derekfountain/zx-spectrum-pico-rom/images/first_fail.jpg

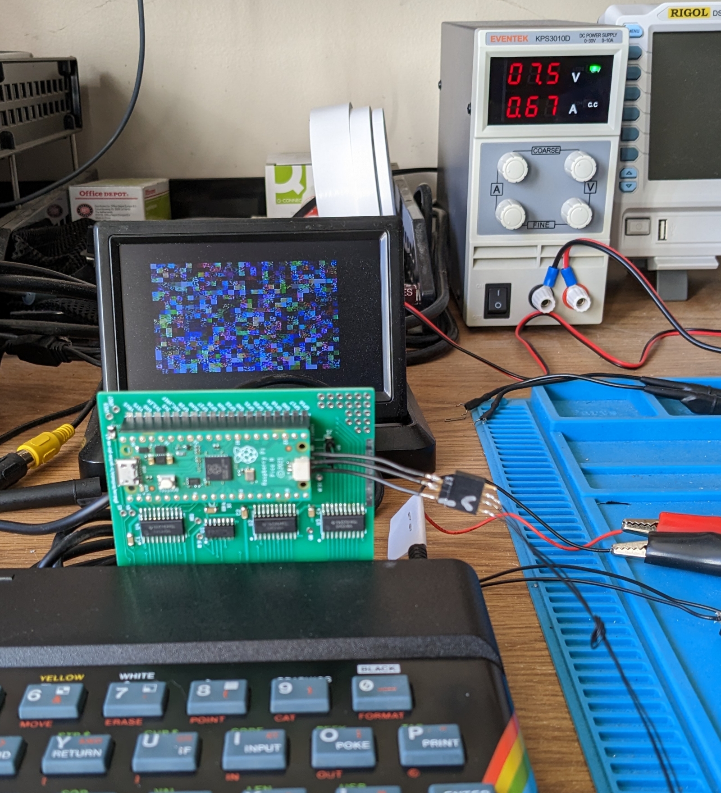
images/first_fail.jpg
