derekfountain/zx-spectrum-pico-rom/images/first_success.jpg

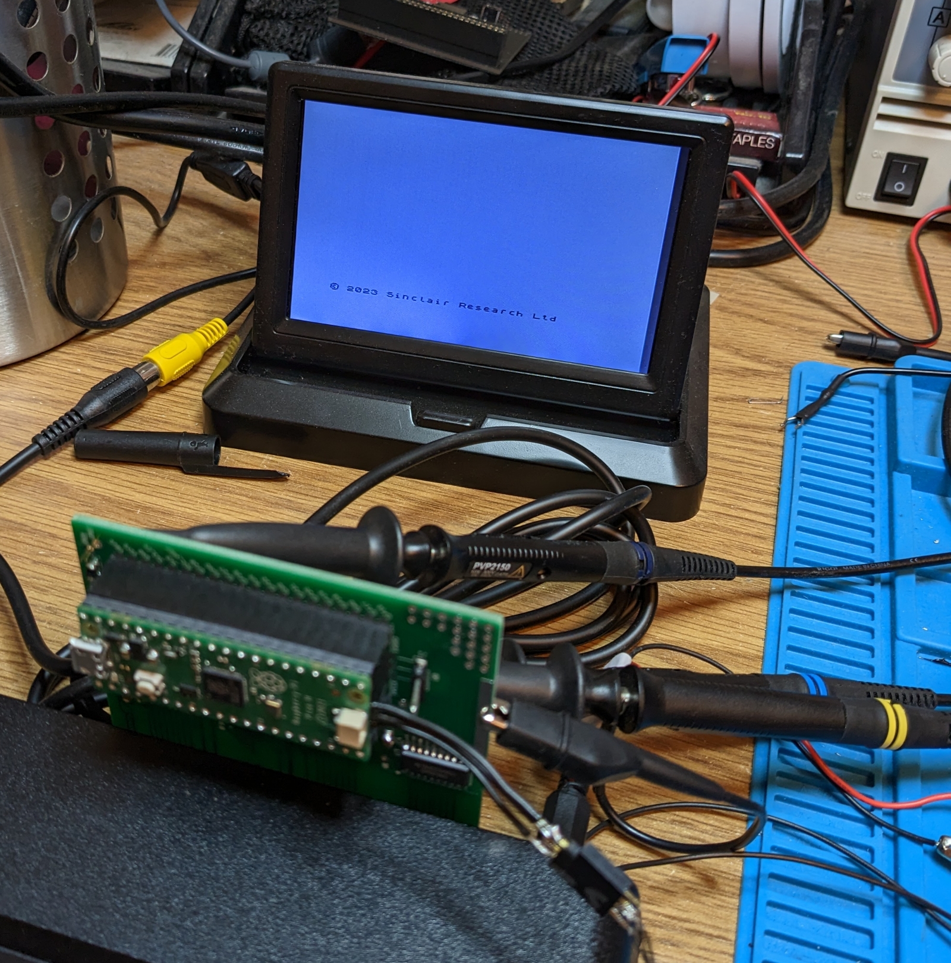
images/first_success.jpg
