derekfountain/zx-spectrum-pico-rom/images/frame_trace_nmi_original.png

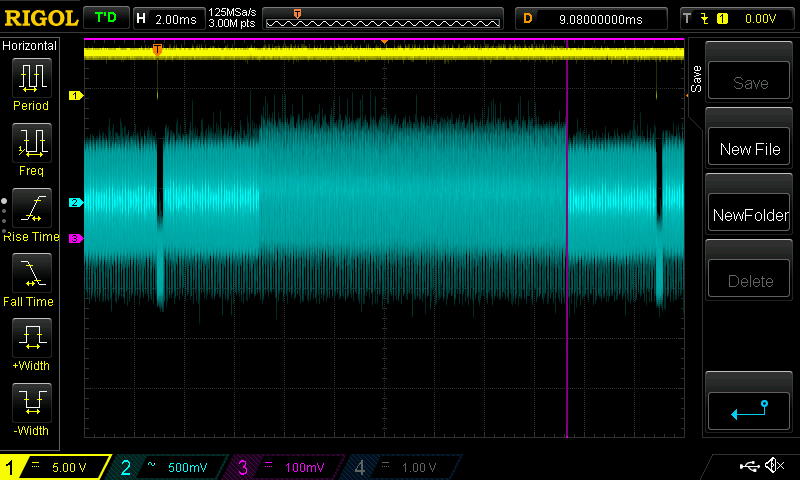
images/frame_trace_nmi_original.png
