derekfountain/zx-spectrum-pico-rom/images/frame_trace_unannotated.png

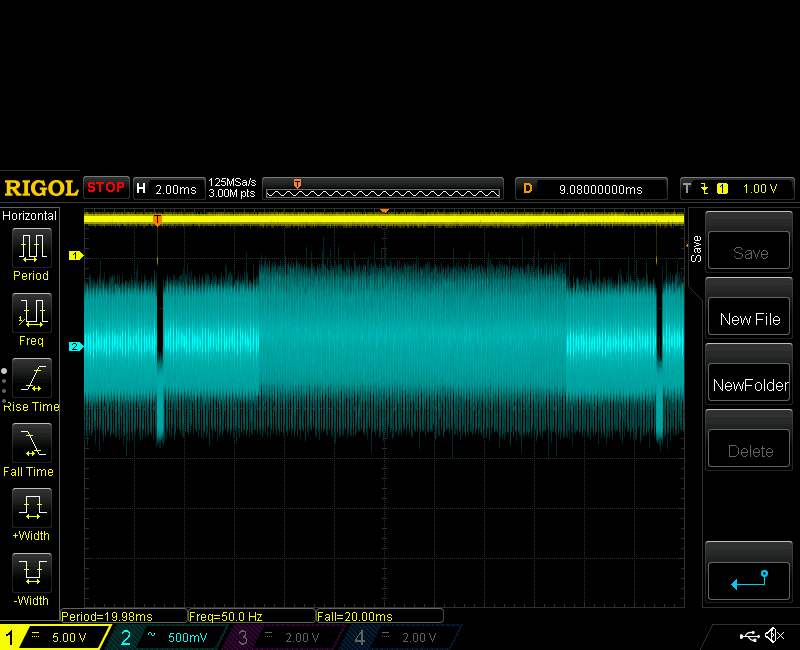
images/frame_trace_unannotated.png
