derekfountain/zx-spectrum-pico-rom/images/PXL_20230126_151511144.jpg

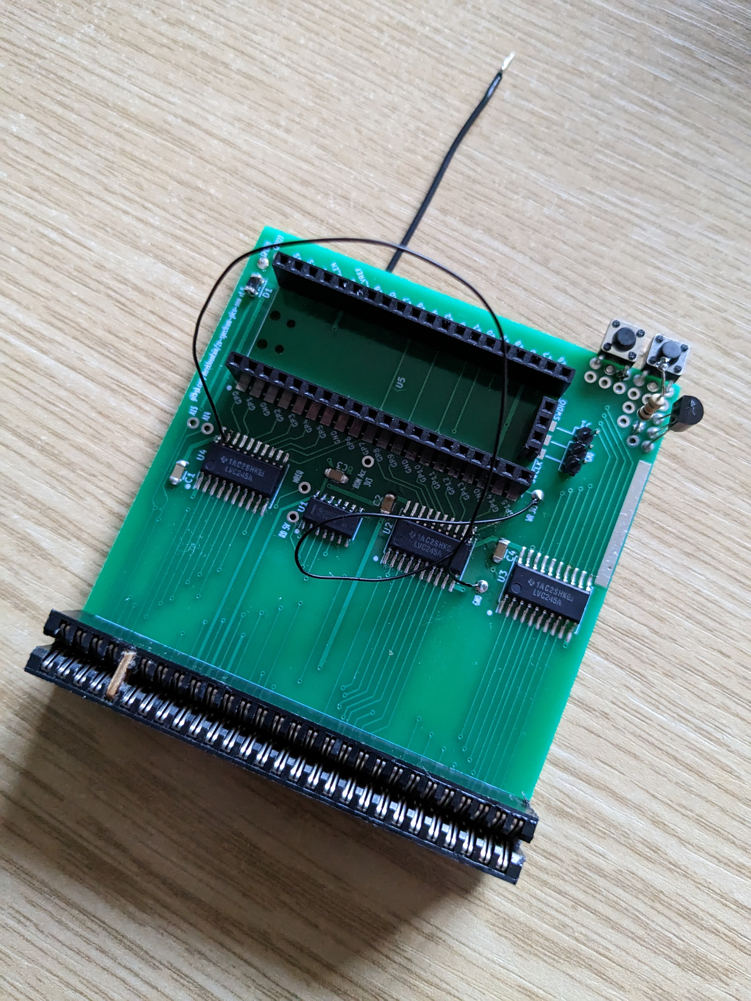
images/PXL_20230126_151511144.jpg
