derekfountain/zx-spectrum-pico-rom/images/second_pcb.jpg

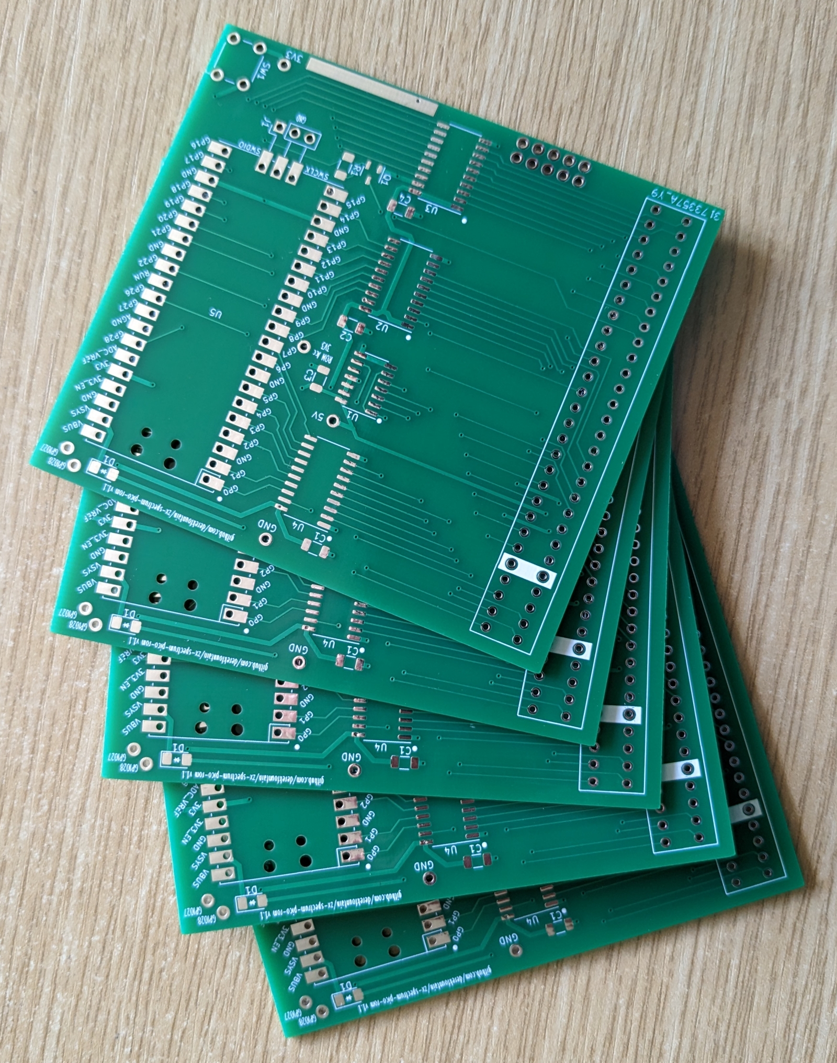
images/second_pcb.jpg
