derekfountain/zx-spectrum-pico-rom/images/second_version.jpg

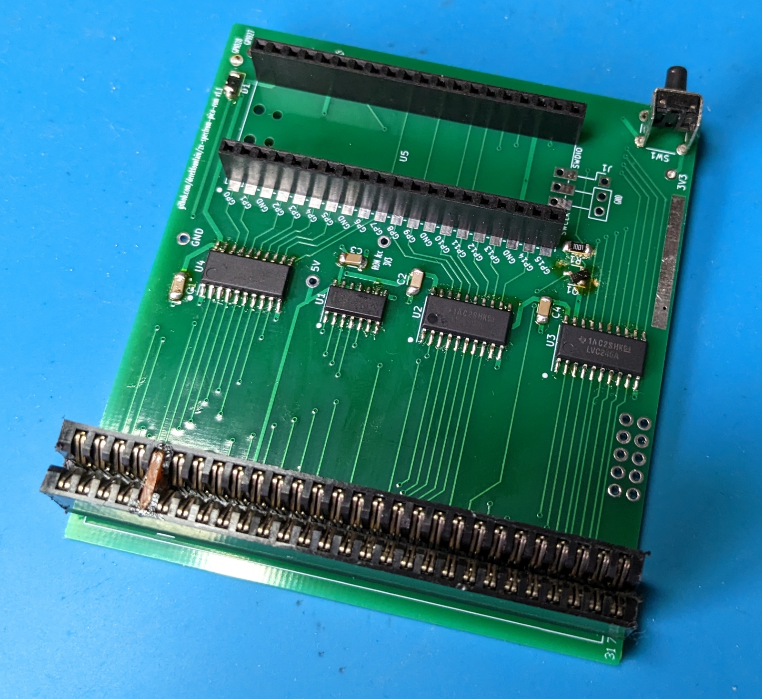
images/second_version.jpg
