derekfountain/zx-spectrum-pico-rom/srom/Images/board_complete.jpg

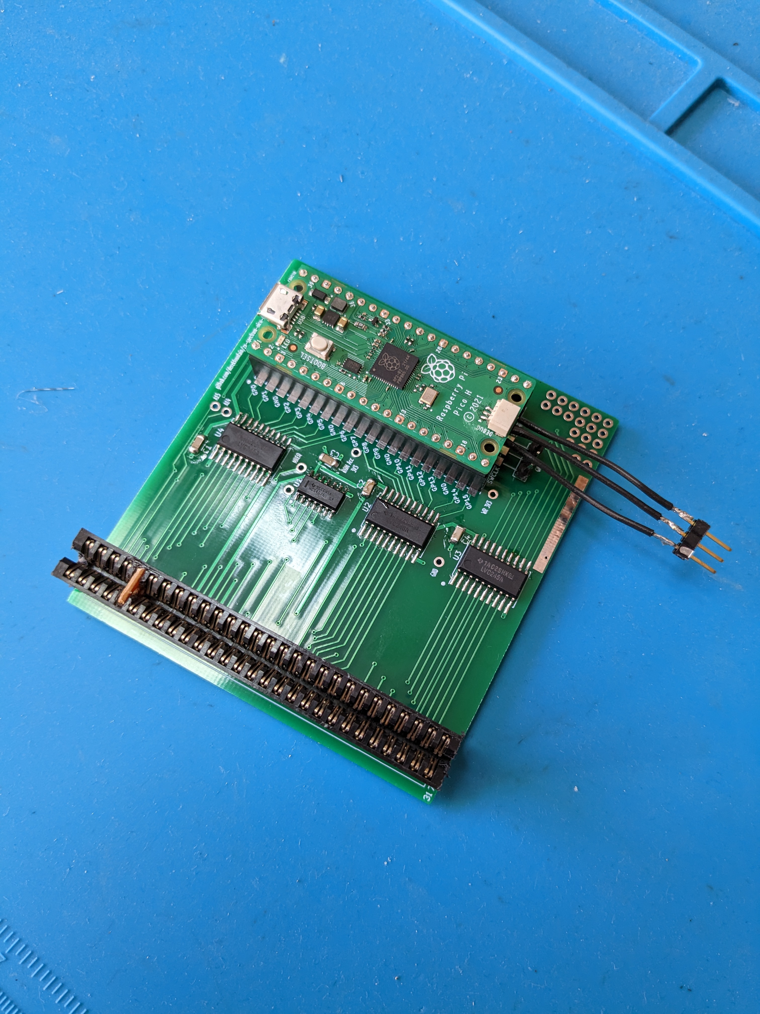
srom/Images/board_complete.jpg
