derekfountain/zx-spectrum-pico-rom/srom/Images/initial_board_powered.jpg

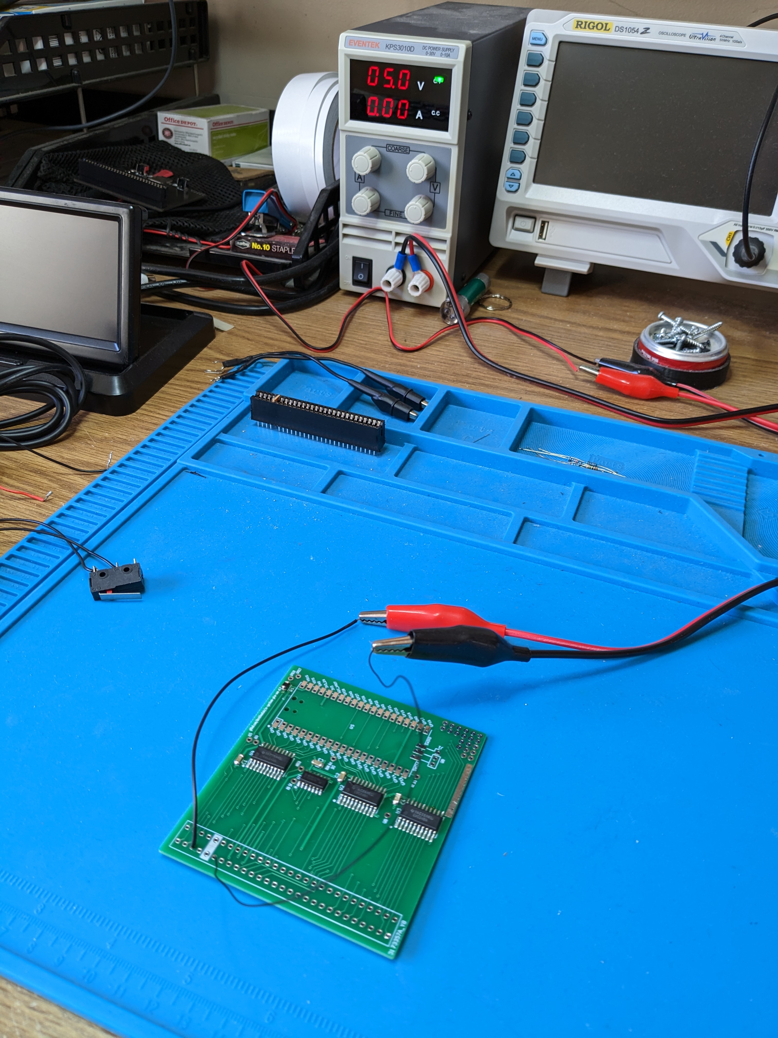
srom/Images/initial_board_powered.jpg
