derekfountain/zx-spectrum-pico-rom/srom/Images/mreq_timing.png

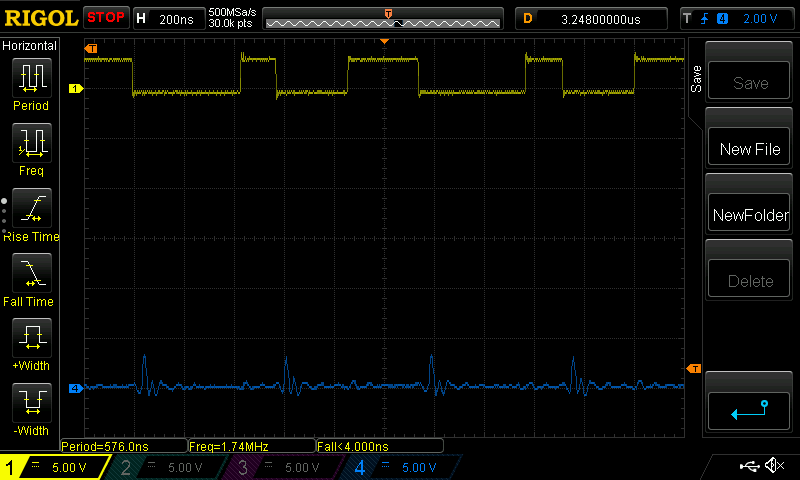
srom/Images/mreq_timing.png
