derekfountain/zx-spectrum-pico-rom/srom/Images/plugged_in_not_working.jpg

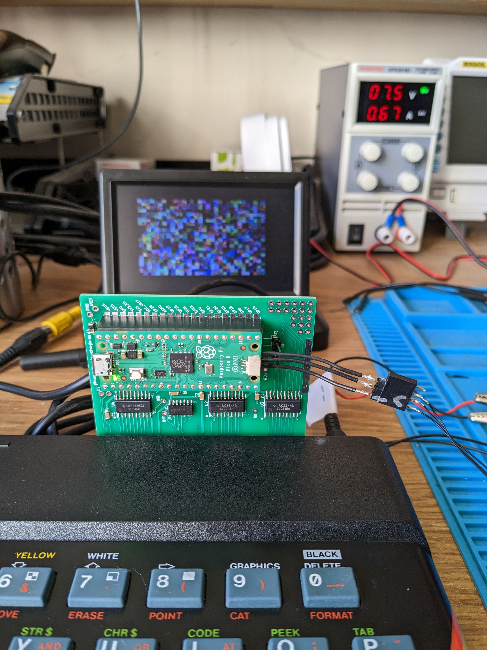
srom/Images/plugged_in_not_working.jpg
