derekfountain/zx-spectrum-pico-rom/images/first_test.jpg

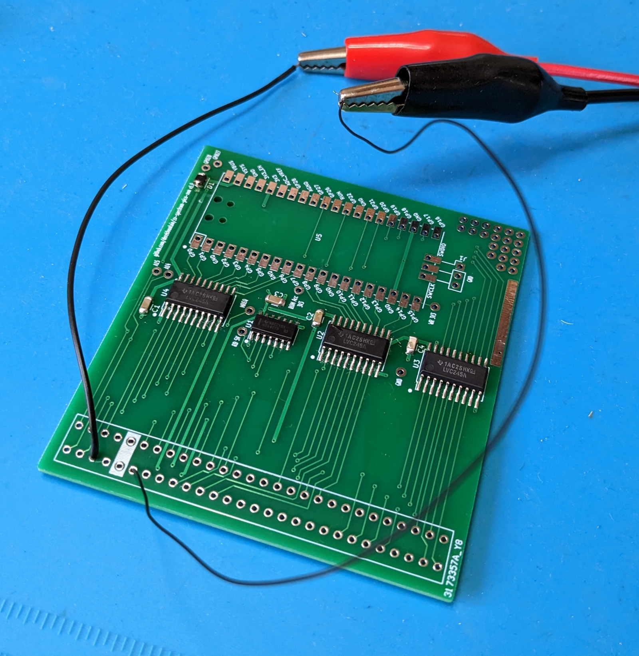
images/first_test.jpg
