derekfountain/zx-spectrum-pico-rom/firmware_nmi_lower_border/roms.h

unsigned char __ROMs_48_original_rom[] = {
  0xf3, 0xaf, 0x11, 0xff, 0xff, 0xc3, 0xcb, 0x11, 0x2a, 0x5d, 0x5c, 0x22,
  0x5f, 0x5c, 0x18, 0x43, 0xc3, 0xf2, 0x15, 0xff, 0xff, 0xff, 0xff, 0xff,
  0x2a, 0x5d, 0x5c, 0x7e, 0xcd, 0x7d, 0x00, 0xd0, 0xcd, 0x74, 0x00, 0x18,
  0xf7, 0xff, 0xff, 0xff, 0xc3, 0x5b, 0x33, 0xff, 0xff, 0xff, 0xff, 0xff,
  0xc5, 0x2a, 0x61, 0x5c, 0xe5, 0xc3, 0x9e, 0x16, 0xf5, 0xe5, 0x2a, 0x78,
  0x5c, 0x23, 0x22, 0x78, 0x5c, 0x7c, 0xb5, 0x20, 0x03, 0xfd, 0x34, 0x40,
  0xc5, 0xd5, 0xcd, 0xbf, 0x02, 0xd1, 0xc1, 0xe1, 0xf1, 0xfb, 0xc9, 0xe1,
  0x6e, 0xfd, 0x75, 0x00, 0xed, 0x7b, 0x3d, 0x5c, 0xc3, 0xc5, 0x16, 0xff,
  0xff, 0xff, 0xff, 0xff, 0xff, 0xff,

   245 ,                // push af
   62  , 3   ,          // ld a, 3
   211 , 254 ,          // out (254),a
   211 , 254 ,          // out (254), a
   62  , 7   ,          // ld a, 7
   211 , 254 ,          // out (254), a
   241 ,                // pop af

  0xed, 0x45,           // retn

                                                  0x2a, 0x5d, 0x5c, 0x23,
  0x22, 0x5d, 0x5c, 0x7e, 0xc9, 0xfe, 0x21, 0xd0, 0xfe, 0x0d, 0xc8, 0xfe,
  0x10, 0xd8, 0xfe, 0x18, 0x3f, 0xd8, 0x23, 0xfe, 0x16, 0x38, 0x01, 0x23,
  0x37, 0x22, 0x5d, 0x5c, 0xc9, 0xbf, 0x52, 0x4e, 0xc4, 0x49, 0x4e, 0x4b,
  0x45, 0x59, 0xa4, 0x50, 0xc9, 0x46, 0xce, 0x50, 0x4f, 0x49, 0x4e, 0xd4,
  0x53, 0x43, 0x52, 0x45, 0x45, 0x4e, 0xa4, 0x41, 0x54, 0x54, 0xd2, 0x41,
  0xd4, 0x54, 0x41, 0xc2, 0x56, 0x41, 0x4c, 0xa4, 0x43, 0x4f, 0x44, 0xc5,
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
  0xaf, 0xb0, 0xb1, 0xc0, 0xa7, 0xa6, 0xbe, 0xad, 0xb2, 0xba, 0xe5, 0xa5,
  0xc2, 0xe1, 0xb3, 0xb9, 0xc1, 0xb8, 0x7e, 0xdc, 0xda, 0x5c, 0xb7, 0x7b,
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
};
unsigned int __ROMs_48_original_rom_len = 16384;
unsigned char *roms[] = {
__ROMs_48_original_rom,
};
