derekfountain/zx-spectrum-pico-rom/firmware/roms.h

#if ZX_IF1_VERSION

unsigned char __ROMs_if1_rom[] = {
  0xe1, 0xfd, 0x36, 0x7c, 0x00, 0xc3, 0x00, 0x07, 0x2a, 0x5d, 0x5c, 0xe1,
  0xe5, 0xc3, 0x9a, 0x00, 0x22, 0xba, 0x5c, 0xe1, 0xd5, 0x18, 0x6a, 0xff,
  0xfd, 0xcb, 0x01, 0x7e, 0xc9, 0xff, 0xff, 0xff, 0xdf, 0x28, 0x45, 0x18,
  0x15, 0xff, 0xff, 0xff, 0xfd, 0xcb, 0x02, 0x9e, 0x18, 0x12, 0xff, 0xff,
  0xc3, 0xf7, 0x01, 0xff, 0xff, 0xff, 0xff, 0xff, 0xfb, 0xc9, 0xcd, 0x77,
  0x00, 0xc3, 0x60, 0x02, 0xdf, 0x28, 0x25, 0xcd, 0x77, 0x00, 0xcd, 0xb7,
  0x17, 0xfd, 0xcb, 0x7c, 0x4e, 0x28, 0x19, 0xfd, 0xcb, 0x7c, 0x66, 0x28,
  0x13, 0xfd, 0x7e, 0x00, 0xfe, 0x14, 0x20, 0x0c, 0x21, 0x00, 0x00, 0xe5,
  0xc7, 0xff, 0xff, 0xff, 0xff, 0xff, 0xed, 0x45, 0x2a, 0x5d, 0x5c, 0x22,
  0x5f, 0x5c, 0xed, 0x7b, 0x3d, 0x5c, 0x21, 0xc5, 0x16, 0xe5, 0xc7, 0xfd,
  0xcb, 0x7c, 0x56, 0xc8, 0xed, 0x7b, 0x3d, 0x5c, 0xc7, 0x5e, 0x23, 0x56,
  0xed, 0x53, 0xbd, 0x5c, 0x23, 0xe3, 0xeb, 0x21, 0x00, 0x00, 0xe5, 0x21,
  0x08, 0x00, 0xe5, 0x21, 0xb9, 0x5c, 0xe5, 0xc3, 0x00, 0x07, 0xf5, 0x7c,
  0xb5, 0x20, 0x06, 0xf1, 0xe1, 0x2a, 0xba, 0x5c, 0xc9, 0xd5, 0x11, 0xfe,
  0x15, 0xed, 0x52, 0xd1, 0x20, 0x0e, 0xf1, 0x21, 0x00, 0x07, 0xe5, 0x21,
  0x04, 0x00, 0x19, 0x5e, 0x23, 0x56, 0xeb, 0xe9, 0xf7, 0x3e, 0x01, 0xd3,
  0xf7, 0x3e, 0xee, 0xd3, 0xef, 0xf1, 0xe1, 0xf5, 0xd7, 0x7b, 0x00, 0x32,
  0x3a, 0x5c, 0xfe, 0xff, 0x20, 0x17, 0xfd, 0xcb, 0x7c, 0x4e, 0x28, 0x0f,
  0xfd, 0xcb, 0x0c, 0x7e, 0x28, 0x09, 0x2a, 0x59, 0x5c, 0x7e, 0xfe, 0xf7,
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
  0x20, 0x20, 0x20, 0x20, 0x20, 0x20, 0x20, 0x00, 0x00, 0x00, 0x00, 0x00,
  0x00, 0x00, 0x00, 0x00, 0x18, 0x18, 0x18, 0x18, 0x00, 0x18, 0x18, 0x00,
  0x6c, 0x6c, 0x48, 0x00, 0x00, 0x00, 0x00, 0x00, 0x36, 0x36, 0x7f, 0x36,
  0xfe, 0x6c, 0x6c, 0x00, 0x7c, 0xd6, 0xd0, 0x7c, 0x16, 0xd6, 0x7c, 0x00,
  0x70, 0xda, 0xdc, 0x78, 0x1e, 0x3b, 0x5b, 0x0e, 0x78, 0xcc, 0xc0, 0x76,
  0xdc, 0xcc, 0x76, 0x00, 0x30, 0x30, 0x20, 0x00, 0x00, 0x00, 0x00, 0x00,
  0x18, 0x30, 0x30, 0x30, 0x30, 0x30, 0x18, 0x00, 0x30, 0x18, 0x18, 0x18,
  0x18, 0x18, 0x30, 0x00, 0x00, 0x24, 0x18, 0x66, 0x18, 0x24, 0x00, 0x00,
  0x00, 0x18, 0x18, 0x7e, 0x18, 0x18, 0x00, 0x00, 0x00, 0x00, 0x00, 0x00,
  0x00, 0x18, 0x18, 0x10, 0x00, 0x00, 0x00, 0xfe, 0x00, 0x00, 0x00, 0x00,
  0x00, 0x00, 0x00, 0x00, 0x00, 0x18, 0x18, 0x00, 0x02, 0x06, 0x0c, 0x18,
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
};
const unsigned int sw_rom_len = 1210;


typedef struct _rom_image
{
  uint8_t  *rom_data;
  uint32_t  rom_size;
  uint8_t  *rom_switcher_label;
} ROM_IMAGE;


#if !ZX_IF1_VERSION

/*
 * This is the list of ROM images which are cycled, in sequence, as the
 * user presses the button for the next ROM
 */
const ROM_IMAGE cycle_roms[] =
{
  {__ROMs_48_original_rom,          __ROMs_48_original_rom_len ,
  "   Retroleum Diagnostics v59    "},

  {__ROMs_retroleum_diag_v59_rom,   __ROMs_retroleum_diag_v59_rom_len ,
  "   GOSH Wonderful ROM v1.32     "},

  {__ROMs_gosh_wonderful_1_32_rom,  __ROMs_gosh_wonderful_1_32_rom_len ,
  " Original ZX Spectrum ROM 1982  "},
};

#else

/*
 * ROMs aren't cycled in the Interface One version but they need to be
 * run through the conversion optimisations so they need to be in this
 * array.
 */
const ROM_IMAGE cycle_roms[] =
{
  {__ROMs_48_original_rom,          __ROMs_48_original_rom_len ,
  "                                "},

  {__ROMs_if1_rom,                  __ROMs_if1_rom_len ,
  "                                "},
};

#endif    /* Interface One version */

uint8_t num_cycle_roms   = (sizeof(cycle_roms)   / sizeof(ROM_IMAGE));
